aentinger/DHT22Childboard/images/dht22-childboard-top-large.jpg

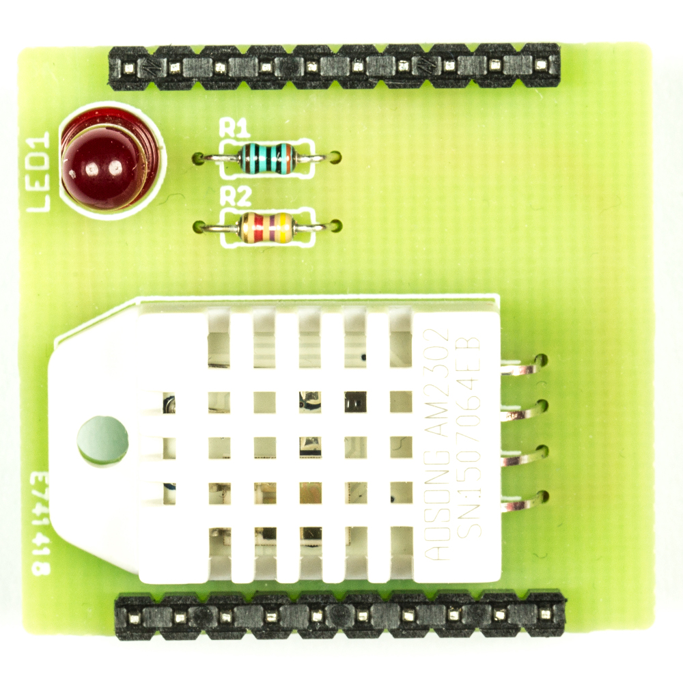
images/dht22-childboard-top-large.jpg
